ouser555/CadMouseMk2_Easy/firmware/include/Controllers.h

#pragma once

#include "controllers/HIDController.h"
#include "controllers/InputController.h"
#include "controllers/LEDController.h"
#include "controllers/MotionController.h"
#include "controllers/SensorController.h"
#include "controllers/TelemetryController.h"

extern InputController inputController;
extern LEDController ledController;
extern SensorController sensorController;
extern MotionController motionController;
extern HIDController hidController;
extern TelemetryController telemetryController;
